SharpCoder/hexagon2/3d/wall-mount.scad

include <config.scad>;

thickness = 20;
h = 116;
w = 5;
tol = .5;
lip = 5;
screw_size = 6;

difference() {
    linear_extrude(thickness)
    union() {        
        square([h, w], center=true);

        translate([-h/2,-(HEX_HEIGHT+tol)/2,0])
        square([w,HEX_HEIGHT+tol+w], center=true);

        translate([-h/2+(lip/2), -(HEX_HEIGHT+tol+w), 0])
        square([w+lip, w], center=true);
    }
    
        
    translate([h/2 - 10, 50, thickness/2])
    union() {
        rotate([90, 90, 0])
        linear_extrude(100)
        circle(d=screw_size + .5, $fn=100);
        
        translate([-screw_size/1.5, 0, 0])
        rotate([90, 90, 0])
        linear_extrude(100)
        circle(d=screw_size + 2, $fn=100);
    }
}
