SharpCoder/hexagon2/3d/washer.scad

linear_extrude(1.5)
difference() {
    circle(d=20);
    circle(d=6.4);
}
