SharpCoder/hexagon2/src/kernel/mem.rs

/*
    Author: Josh Cole
    This library is dedicated to managing memory.
*/
#![allow(dead_code, unused_imports)]

use core::mem::{size_of};
use crate::phys::*;
use crate::phys::addrs::OCRAM2;

const MEMORY_MAXIMUM: u32 = 0x7_FFFF; // 512kb
const MEMORY_BEGIN_OFFSET: u32 = 0x0_FFC; // 4kb buffer (note: it should be word aligned)
static mut MEMORY_OFFSET: u32 = MEMORY_BEGIN_OFFSET;

pub fn alloc(bytes: usize) -> *mut u32 {
    // Check for boundaries and reset if applicable.
    unsafe {
        if MEMORY_OFFSET + bytes as u32 > MEMORY_MAXIMUM {
            MEMORY_OFFSET = MEMORY_BEGIN_OFFSET;
            crate::err();
        }

        let ptr = (OCRAM2 + MEMORY_OFFSET) as *mut u32;
        MEMORY_OFFSET += bytes as u32;
        return ptr;
    }
}

/// This is kernal alloc and it implements what I call a "cyclical mempage strategy".
/// Memory is constantly allocated in RAM and eventually will loop back around
/// if all memory is used up. Clearly, this is a bad idea. Will be improved over time.
pub fn kalloc<T>() -> *mut T {
    let bytes = size_of::<T>();
    return alloc(bytes) as *mut T;
}

/// Free a pointer by updating the pagefile
pub fn free<T>(ptr: *mut T) {
    let bytes = size_of::<T>() as u32;
    let zero_ptr = ptr as u32;
    for i in 0u32 .. (bytes / 4) {
        assign(zero_ptr + (i * 4), 0);
    }
}
